AndreaRoss96/Smart_Green_House/green_house_controller/greenhousecontrollerino/FadingLed.h

#ifndef __FADINGLED__
#define __FADINGLED__

#include "Light.h"
#include "LevelIndicator.h"

/*fadingled è un indicatore di livello che implementa l'interfaccia
* LevelIndicator
*/
class FadingLed : public LevelIndicator{
public:
  FadingLed(int pin);
  void switchOn();
  void switchOff();
  void setLevel(int lvl);
  void toggle();
private:
  int pin;
  int status;
  int level;
};

#endif
