AndreaRoss96/Smart_Green_House/green_house_controller/greenhousecontrollerino/GlobalClass.h

#ifndef __GLOBALCLASS__
#define __GLOBALCLASS__

#include "Arduino.h"

#define DIST  0.3
#define NOFLOW 0
#define LOWFLOW 20
#define MEDIUMFLOW 50
#define HIGHFLOW 100
/*
Classe globale in singleton che contiene le informazioni generali del sistema
come umidita, flow (livello di apertura della pompa), modalità del sistema
manuale o automatica) e le costanti del sistema sotto forma di macro */


class GlobalClass { //SINGLETON


  private:
      GlobalClass() {}

      bool automatic = true;
      int flow = 0;
      int humidity = 0;
      bool connected = false;

  public:
    /*
    return
      The instance of the globalClass
    */
    static GlobalClass& getInstance() {
        static GlobalClass gbInstance;
        return gbInstance;
    }


    void setFlow(int f){ flow = f; }
    void setHumidity(int h){ humidity = h; }
    void toggleAutomode(){ automatic = !automatic;}
    void toggleConnection(){ connected = !connected; }

    float getEngagementDist(){ return DIST;   } 
    int getFlow(){ return flow;  }
    int getHumidity(){ return humidity;  }
    bool isAutoMode(){ return automatic;  }
    bool isConnected(){ return connected;  }



};
#endif
