AndreaRoss96/Smart_Green_House/green_house_controller/greenhousecontrollerino/TaskSearch.h

#ifndef __TASKSEARCH__
#define __TASKSEARCH__

#include "Task.h"
#include "Sensor.h"
#include "Light.h"

/*task che controlla se l'utente è abbastanza vicino da potersi
* connettere con il bluetooth
*/
class TaskSearch: public Task{
  public:
    TaskSearch(Sensor *prox, Light *la, Light *lm);
    void tick();
    void init(int period);

  private:
    Light *la, *lm;
    Sensor *prox;
    int timeElapsed;
};

#endif
